SP8EBC/radio-usb-interface/_output_files/hw_rev_b/Screenshot 2024-08-04 at 09-53-23 JLCPCB PCBA Viewer.png

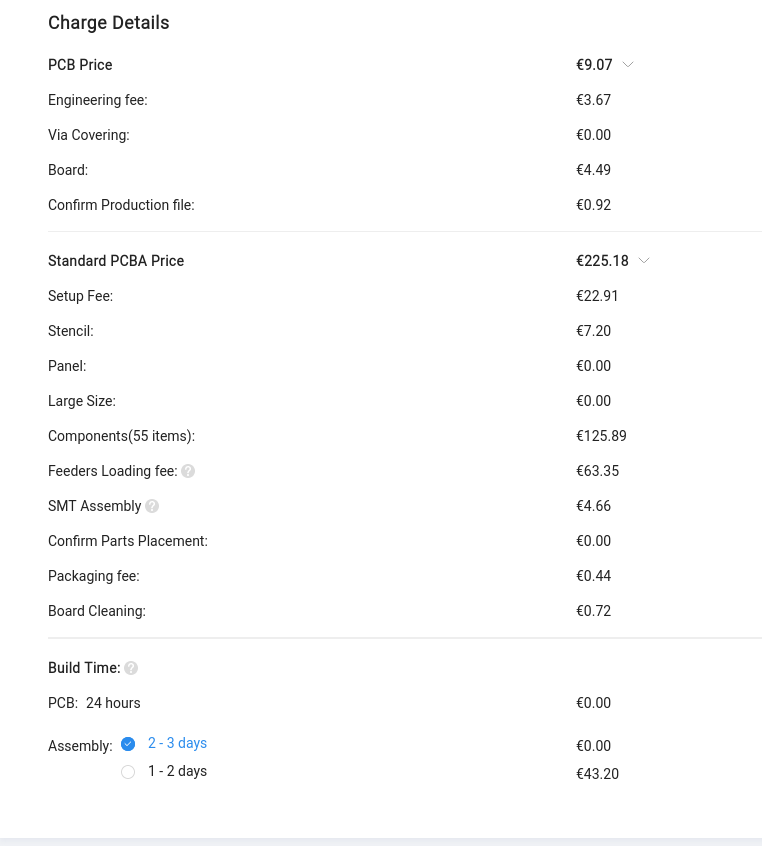
_output_files/hw_rev_b/Screenshot 2024-08-04 at 09-53-23 JLCPCB PCBA Viewer.png
