SP8EBC/radio-usb-interface/_output_files/hw_rev_b/Screenshot 2024-08-04 at 09-55-26 PCB Prototype & PCB F[...].png

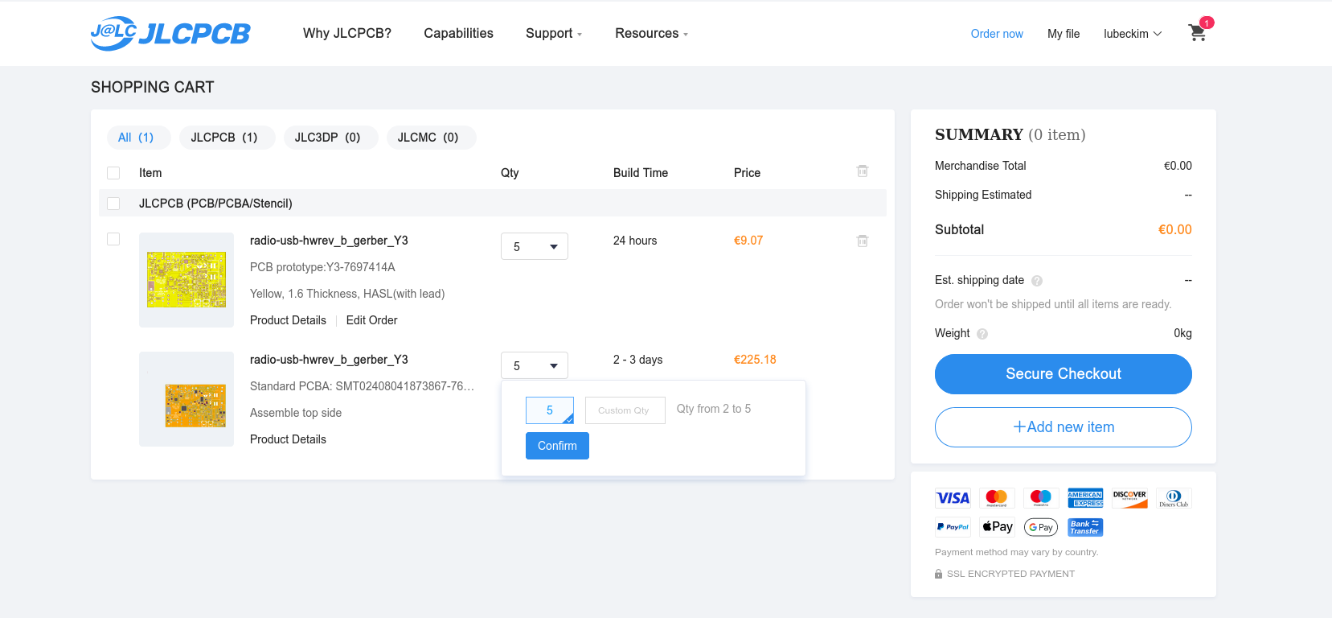
_output_files/hw_rev_b/Screenshot 2024-08-04 at 09-55-26 PCB Prototype & PCB F[...].png
