SP8EBC/radio-usb-interface/_output_files/hw_rev_b/___jlpcb/final_production_files_from_jlpcb_after_bom_adjusting/85564153487360-Produce_DanZhi.SMT_Snapshot.Top.7697414A_Y3.SMT02408041873867.png

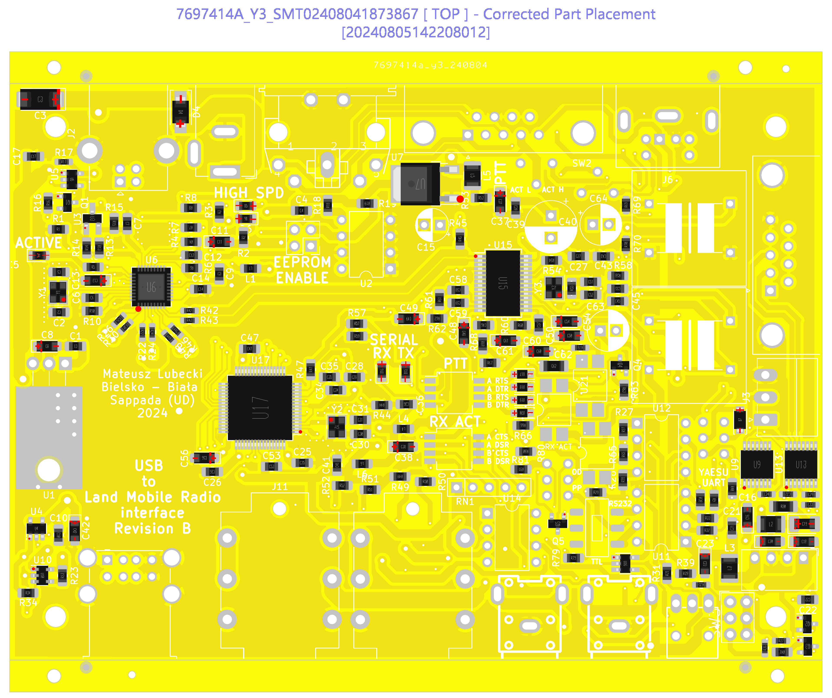
_output_files/hw_rev_b/___jlpcb/final_production_files_from_jlpcb_after_bom_adjusting/85564153487360-Produce_DanZhi.SMT_Snapshot.Top.7697414A_Y3.SMT02408041873867.png
